ayuusweetfish/Canta-Cart/misc/synth/canta_synth.h

#pragma once

#include <stdbool.h>
#include <stdint.h>
#include <stdio.h>
#include <string.h>

#ifndef SYNTH_SAMPLE_RATE
  #define SYNTH_SAMPLE_RATE 44100
#endif
#ifndef SYNTH_EXTRA_SHIFT
  #define SYNTH_EXTRA_SHIFT 1
#endif

#define SYNTH_ATTACK_INCR   (int)((1 << 15) / (SYNTH_SAMPLE_RATE * 0.025))
#define SYNTH_RELEASE_INCR  (int)((1 << 15) / (SYNTH_SAMPLE_RATE * 0.075))

static int8_t key_base = 0;
static int8_t scale_base = 0;

// MIDI note:
// Max. 71 + (n + scale_base) (+23 scale degrees, +40) + key_base (+12) + transpose (+1) = 124
// Min. 71 + (n + scale_base) (-18 scale degrees, -31) + key_base (-12) + transpose (-1) = 27

// Period = f_s/f samples = 2^32 in lookup table
// Increment for each sample = 2^32 / (f_s/f)
// note_freq[i] =
//   4294967296.0 * (440.0 * pow(2, (i - 69) / 12.0)) / SYNTH_SAMPLE_RATE
static const uint32_t note_freq[128] = {
  // print('\n'.join('  (uint32_t)(%.4f / SYNTH_SAMPLE_RATE + 0.5),' % (4294967296.0 * (440.0 * (2 ** ((i - 69) / 12.0)))) for i in range(128)))
  (uint32_t)(35114788961.3620 / SYNTH_SAMPLE_RATE + 0.5),
  (uint32_t)(37202822970.7782 / SYNTH_SAMPLE_RATE + 0.5),
  (uint32_t)(39415017943.5217 / SYNTH_SAMPLE_RATE + 0.5),
  (uint32_t)(41758756874.6707 / SYNTH_SAMPLE_RATE + 0.5),
  (uint32_t)(44241861775.0361 / SYNTH_SAMPLE_RATE + 0.5),
  (uint32_t)(46872619776.3960 / SYNTH_SAMPLE_RATE + 0.5),
  (uint32_t)(49659810789.0272 / SYNTH_SAMPLE_RATE + 0.5),
  (uint32_t)(52612736803.8398 / SYNTH_SAMPLE_RATE + 0.5),
  (uint32_t)(55741252936.9073 / SYNTH_SAMPLE_RATE + 0.5),
  (uint32_t)(59055800320.0000 / SYNTH_SAMPLE_RATE + 0.5),
  (uint32_t)(62567440946.8918 / SYNTH_SAMPLE_RATE + 0.5),
  (uint32_t)(66287894591.7365 / SYNTH_SAMPLE_RATE + 0.5),
  (uint32_t)(70229577922.7240 / SYNTH_SAMPLE_RATE + 0.5),
  (uint32_t)(74405645941.5564 / SYNTH_SAMPLE_RATE + 0.5),
  (uint32_t)(78830035887.0435 / SYNTH_SAMPLE_RATE + 0.5),
  (uint32_t)(83517513749.3414 / SYNTH_SAMPLE_RATE + 0.5),
  (uint32_t)(88483723550.0722 / SYNTH_SAMPLE_RATE + 0.5),
  (uint32_t)(93745239552.7919 / SYNTH_SAMPLE_RATE + 0.5),
  (uint32_t)(99319621578.0543 / SYNTH_SAMPLE_RATE + 0.5),
  (uint32_t)(105225473607.6797 / SYNTH_SAMPLE_RATE + 0.5),
  (uint32_t)(111482505873.8147 / SYNTH_SAMPLE_RATE + 0.5),
  (uint32_t)(118111600640.0000 / SYNTH_SAMPLE_RATE + 0.5),
  (uint32_t)(125134881893.7837 / SYNTH_SAMPLE_RATE + 0.5),
  (uint32_t)(132575789183.4730 / SYNTH_SAMPLE_RATE + 0.5),
  (uint32_t)(140459155845.4479 / SYNTH_SAMPLE_RATE + 0.5),
  (uint32_t)(148811291883.1128 / SYNTH_SAMPLE_RATE + 0.5),
  (uint32_t)(157660071774.0869 / SYNTH_SAMPLE_RATE + 0.5),
  (uint32_t)(167035027498.6827 / SYNTH_SAMPLE_RATE + 0.5),
  (uint32_t)(176967447100.1444 / SYNTH_SAMPLE_RATE + 0.5),
  (uint32_t)(187490479105.5839 / SYNTH_SAMPLE_RATE + 0.5),
  (uint32_t)(198639243156.1087 / SYNTH_SAMPLE_RATE + 0.5),
  (uint32_t)(210450947215.3594 / SYNTH_SAMPLE_RATE + 0.5),
  (uint32_t)(222965011747.6293 / SYNTH_SAMPLE_RATE + 0.5),
  (uint32_t)(236223201280.0000 / SYNTH_SAMPLE_RATE + 0.5),
  (uint32_t)(250269763787.5674 / SYNTH_SAMPLE_RATE + 0.5),
  (uint32_t)(265151578366.9460 / SYNTH_SAMPLE_RATE + 0.5),
  (uint32_t)(280918311690.8959 / SYNTH_SAMPLE_RATE + 0.5),
  (uint32_t)(297622583766.2255 / SYNTH_SAMPLE_RATE + 0.5),
  (uint32_t)(315320143548.1738 / SYNTH_SAMPLE_RATE + 0.5),
  (uint32_t)(334070054997.3655 / SYNTH_SAMPLE_RATE + 0.5),
  (uint32_t)(353934894200.2888 / SYNTH_SAMPLE_RATE + 0.5),
  (uint32_t)(374980958211.1677 / SYNTH_SAMPLE_RATE + 0.5),
  (uint32_t)(397278486312.2173 / SYNTH_SAMPLE_RATE + 0.5),
  (uint32_t)(420901894430.7188 / SYNTH_SAMPLE_RATE + 0.5),
  (uint32_t)(445930023495.2587 / SYNTH_SAMPLE_RATE + 0.5),
  (uint32_t)(472446402560.0000 / SYNTH_SAMPLE_RATE + 0.5),
  (uint32_t)(500539527575.1349 / SYNTH_SAMPLE_RATE + 0.5),
  (uint32_t)(530303156733.8922 / SYNTH_SAMPLE_RATE + 0.5),
  (uint32_t)(561836623381.7917 / SYNTH_SAMPLE_RATE + 0.5),
  (uint32_t)(595245167532.4510 / SYNTH_SAMPLE_RATE + 0.5),
  (uint32_t)(630640287096.3478 / SYNTH_SAMPLE_RATE + 0.5),
  (uint32_t)(668140109994.7310 / SYNTH_SAMPLE_RATE + 0.5),
  (uint32_t)(707869788400.5775 / SYNTH_SAMPLE_RATE + 0.5),
  (uint32_t)(749961916422.3354 / SYNTH_SAMPLE_RATE + 0.5),
  (uint32_t)(794556972624.4347 / SYNTH_SAMPLE_RATE + 0.5),
  (uint32_t)(841803788861.4374 / SYNTH_SAMPLE_RATE + 0.5),
  (uint32_t)(891860046990.5173 / SYNTH_SAMPLE_RATE + 0.5),
  (uint32_t)(944892805120.0000 / SYNTH_SAMPLE_RATE + 0.5),
  (uint32_t)(1001079055150.2698 / SYNTH_SAMPLE_RATE + 0.5),
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
  (uint32_t)(45303666457636.9531 / SYNTH_SAMPLE_RATE + 0.5),
  (uint32_t)(47997562651029.4766 / SYNTH_SAMPLE_RATE + 0.5),
  (uint32_t)(50851646247963.8203 / SYNTH_SAMPLE_RATE + 0.5),
  (uint32_t)(53875442487131.9844 / SYNTH_SAMPLE_RATE + 0.5),
};

static inline uint32_t freq_for_note(int8_t n, int8_t key_base, int8_t transpose)
{
  int octave = (n < 0 ? (n - 6) / 7 : n / 7);
  int degree = n - octave * 7;
  static const uint8_t scale[7] = {0, 2, 4, 5, 7, 9, 11};
  int midi_pitch = 71 + key_base + (octave * 12 + scale[degree]) + transpose;
  return note_freq[midi_pitch];
}

static struct {
  uint32_t freq;
  uint32_t phase;

  uint16_t state; // 0: idle; 1: attack/decay; 2: sustain; 3: release
  uint16_t time;
} keys[10];

static bool last_btn[12] = { 0 };

// Whether a note has been pressed during the time when the transpose key is held
static bool transp_used[2];

#ifdef SYNTH_SINE
static int16_t sine_table[4096] = {
// from math import sin, pi, floor; print(', '.join('%d' % floor(32767.5 * sin(i / 4096.0 * 2 * pi)) for i in range(4096)))
0, 50, 100, 150, 201, 251, 301, 351, 402, 452, 502, 552, 603, 653, 703, 753, 804, 854, 904, 954, 1005, 1055, 1105, 1155, 1206, 1256, 1306, 1356, 1406, 1457, 1507, 1557, 1607, 1658, 1708, 1758, 1808, 1858, 1908, 1959, 2009, 2059, 2109, 2159, 2209, 2260, 2310, 2360, 2410, 2460, 2510, 2560, 2610, 2661, 2711, 2761, 2811, 2861, 2911, 2961, 3011, 3061, 3111, 3161, 3211, 3261, 3311, 3361, 3411, 3461, 3511, 3561, 3611, 3661, 3711, 3761, 3811, 3861, 3911, 3961, 4011, 4060, 4110, 4160, 4210, 4260, 4310, 4360, 4409, 4459, 4509, 4559, 4609, 4658, 4708, 4758, 4807, 4857, 4907, 4957, 5006, 5056, 5106, 5155, 5205, 5255, 5304, 5354, 5403, 5453, 5502, 5552, 5601, 5651, 5701, 5750, 5799, 5849, 5898, 5948, 5997, 6047, 6096, 6145, 6195, 6244, 6293, 6343, 6392, 6441, 6491, 6540, 6589, 6638, 6688, 6737, 6786, 6835, 6884, 6933, 6983, 7032, 7081, 7130, 7179, 7228, 7277, 7326, 7375, 7424, 7473, 7522, 7571, 7620, 7668, 7717, 7766, 7815, 7864, 7913, 7961, 8010, 8059, 8108, 8156, 8205, 8254, 8302, 8351, 8399, 8448, 8497, 8545, 8594, 8642, 8691, 8739, 8787, 8836, 8884, 8933, 8981, 9029, 9078, 9126, 9174, 9222, 9271, 9319, 9367, 9415, 9463, 9511, 9559, 9608, 9656, 9704, 9752, 9800, 9848, 9895, 9943, 9991, 10039, 10087, 10135, 10183, 10230, 10278, 10326, 10373, 10421, 10469, 10516, 10564, 10612, 10659, 10707, 10754, 10802, 10849, 10896, 10944, 10991, 11039, 11086, 11133, 11180, 11228, 11275, 11322, 11369, 11416, 11463, 11510, 11558, 11605, 11652, 11699, 11745, 11792, 11839, 11886, 11933, 11980, 12026, 1207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
};
#endif

static inline int16_t synth_table(uint32_t phase)
{
#ifdef SYNTH_SINE
  return sine_table[phase >> 20] >> (4 + SYNTH_EXTRA_SHIFT);
#else
  return (phase < (1u << 31) ?
      (int32_t)((1u << 31) + phase * 2) :
      (int32_t)(((1u << 31) - 1) - (phase - (1u << 31)) * 2)
    ) >> (16 /* Max. range */ + 4 /* Avoid clipping with polyphony 10 */ + SYNTH_EXTRA_SHIFT);
#endif
}

#ifdef SYNTH_STEREO
  #define N_CH 2
#else
  #define N_CH 1
#endif
static inline void synth_audio(int16_t *buf, uint32_t count)
{
  memset(buf, 0, count * sizeof(int16_t));
  for (int i = 0; i < 10; i++) if (keys[i].state != 0) {
    int j = 0;
    while (j < count && keys[i].state != 0) {
      if (__builtin_expect(keys[i].state == 1, 0)) {
        for (; j < count; j += N_CH) {
          int16_t value = synth_table(keys[i].phase += keys[i].freq);
          keys[i].time += SYNTH_ATTACK_INCR;
          if (__builtin_expect(keys[i].time >= (1 << 15), 0)) {
            buf[j] += value;
            keys[i].state = 2;
            j += N_CH;
            break;
          } else {
            buf[j] += ((int32_t)value * keys[i].time) >> 15;
          }
        }
      } else if (__builtin_expect(keys[i].state == 3, 0)) {
        for (; j < count; j += N_CH) {
          int16_t value = synth_table(keys[i].phase += keys[i].freq);
          keys[i].time += SYNTH_RELEASE_INCR;
          if (__builtin_expect(keys[i].time >= (1 << 15), 0)) {
            keys[i].state = 0;
            j += N_CH;
            break;
          } else {
            buf[j] += ((int32_t)value * ((1 << 15) - keys[i].time)) >> 15;
          }
        }
      } else {
        for (; j < count; j += N_CH) {
          int16_t value = synth_table(keys[i].phase += keys[i].freq);
          buf[j] += value;
        }
      }
    }
  }
}
#undef N_CH

static inline void synth_buttons(bool btn[12])
{
  for (int i = 11; i >= 0; i--) {
    if (btn[i] && !last_btn[i]) {
      // Press
      if (i < 10) {
        int transpose = 0;
        if (btn[10]) { transpose -= 1; transp_used[0] = true; }
        if (btn[11]) { transpose += 1; transp_used[1] = true; }
        keys[i].freq = freq_for_note(scale_base + i, key_base, transpose);
        keys[i].phase = 0;
        keys[i].state = 1;
        keys[i].time = 0;
      } else {
        transp_used[i - 10] = false;
      }
    } else if (!btn[i] && last_btn[i]) {
      // Release
      if (i < 10) {
        keys[i].state = 3;
        keys[i].time = 0;
      } else {
        // If no note has been pressed during the hold,
        // carry out a global transposition
        if (!transp_used[i - 10]) {
          if (btn[i ^ 1]) {
            // Key change
            key_base += (i == 10 ? -1 : +1);
            if (key_base < -12) key_base = -12;
            if (key_base >  12) key_base =  12;
            transp_used[(i - 10) ^ 1] = true;
          } else {
            // Scale base change
            scale_base += (i == 10 ? -1 : +1);
            if (scale_base < -18) scale_base = -18;
            if (scale_base >  14) scale_base =  14;
          }
        }
      }
    }
    last_btn[i] = btn[i];
  }
}
